Wolfman-F16/uhfIndicationPro/firmware/shift.h

/*
 * shift.h
 *
 *  Created on: 30.01.2010
 *      Author: Wolfman
 */

#ifndef SHIFT_H_
#define SHIFT_H_

/****************************   FUNCTION DECLARATIONS ************************/
void loadFreqByte(uint16_t );
void loadChanByte(uint8_t );

void acceptByte(void);

#endif /* SHIFT_H_ */
